softegg/Talkie-DIY-Synth-Kit/docs/PCB Front + back everything.PNG

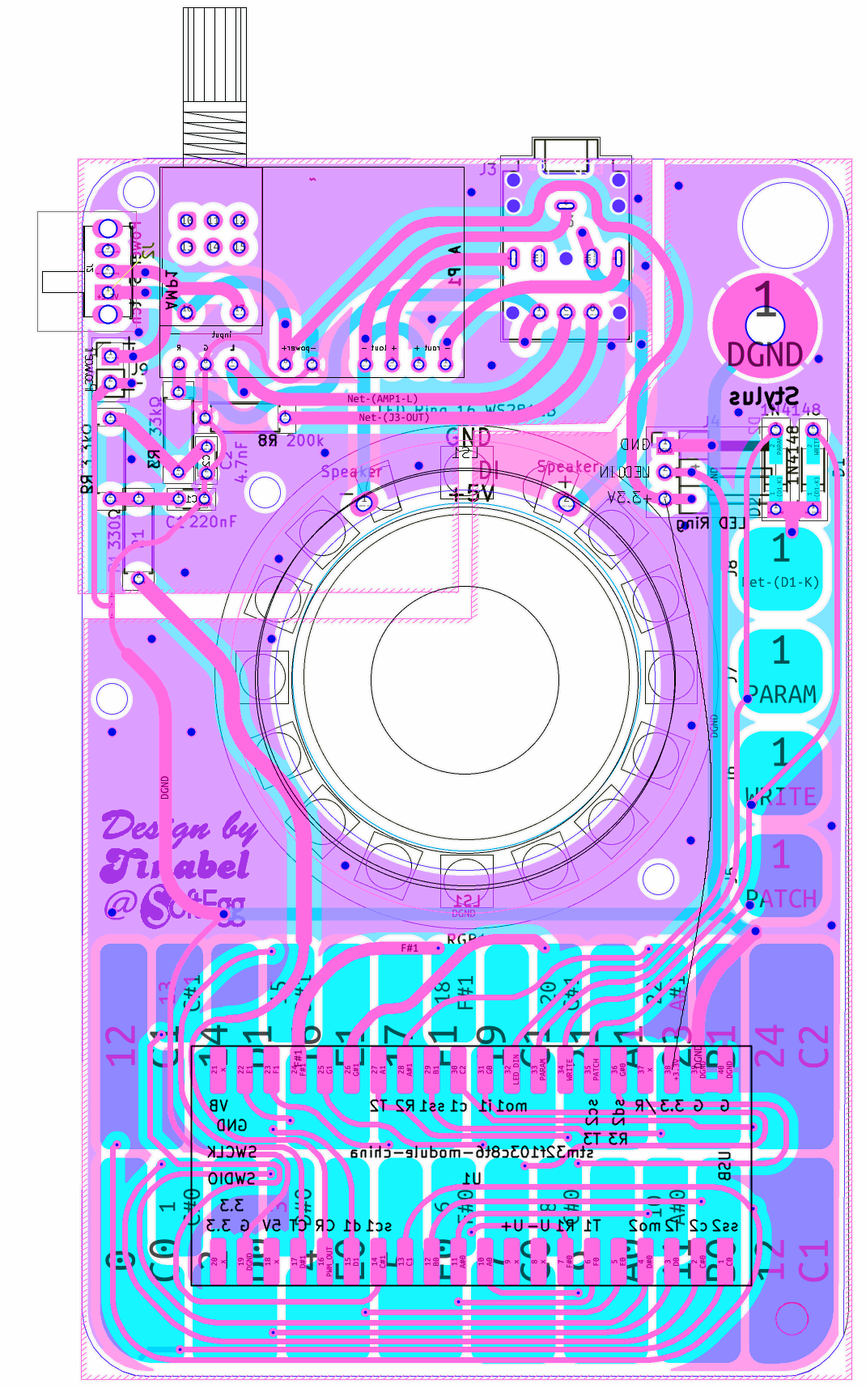
docs/PCB Front + back everything.PNG
