softegg/Talkie-DIY-Synth-Kit/renders/X-DaysSynth-Back.png

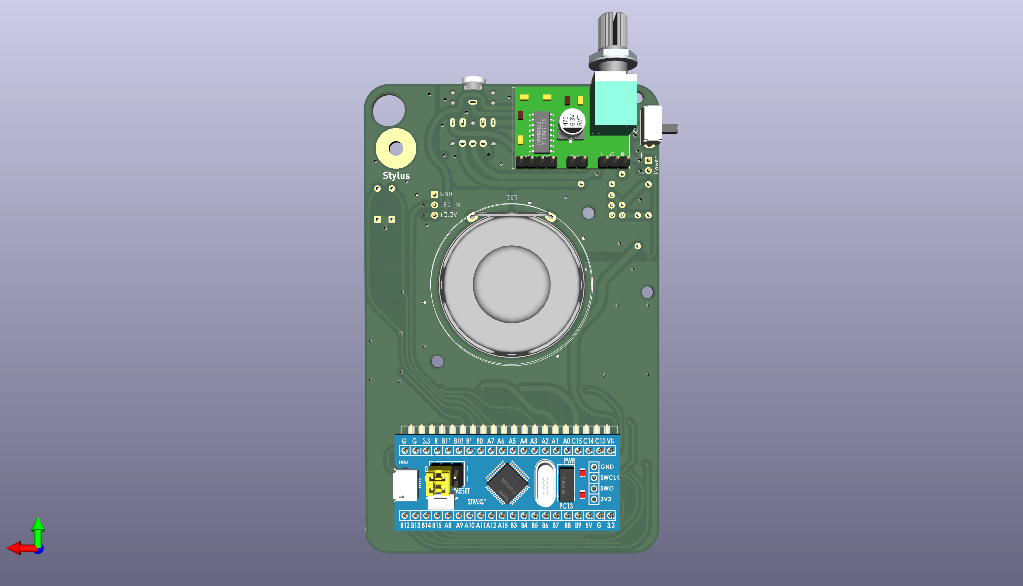
renders/X-DaysSynth-Back.png
