softegg/Talkie-DIY-Synth-Kit/renders/X-DaysSynth-Front-transparent.png

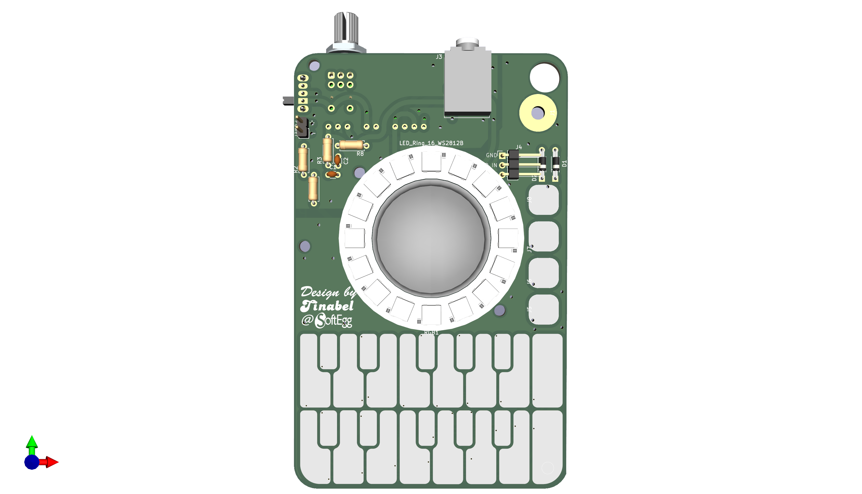
renders/X-DaysSynth-Front-transparent.png
