softegg/Talkie-DIY-Synth-Kit/docs/Back Parts Placement.PNG

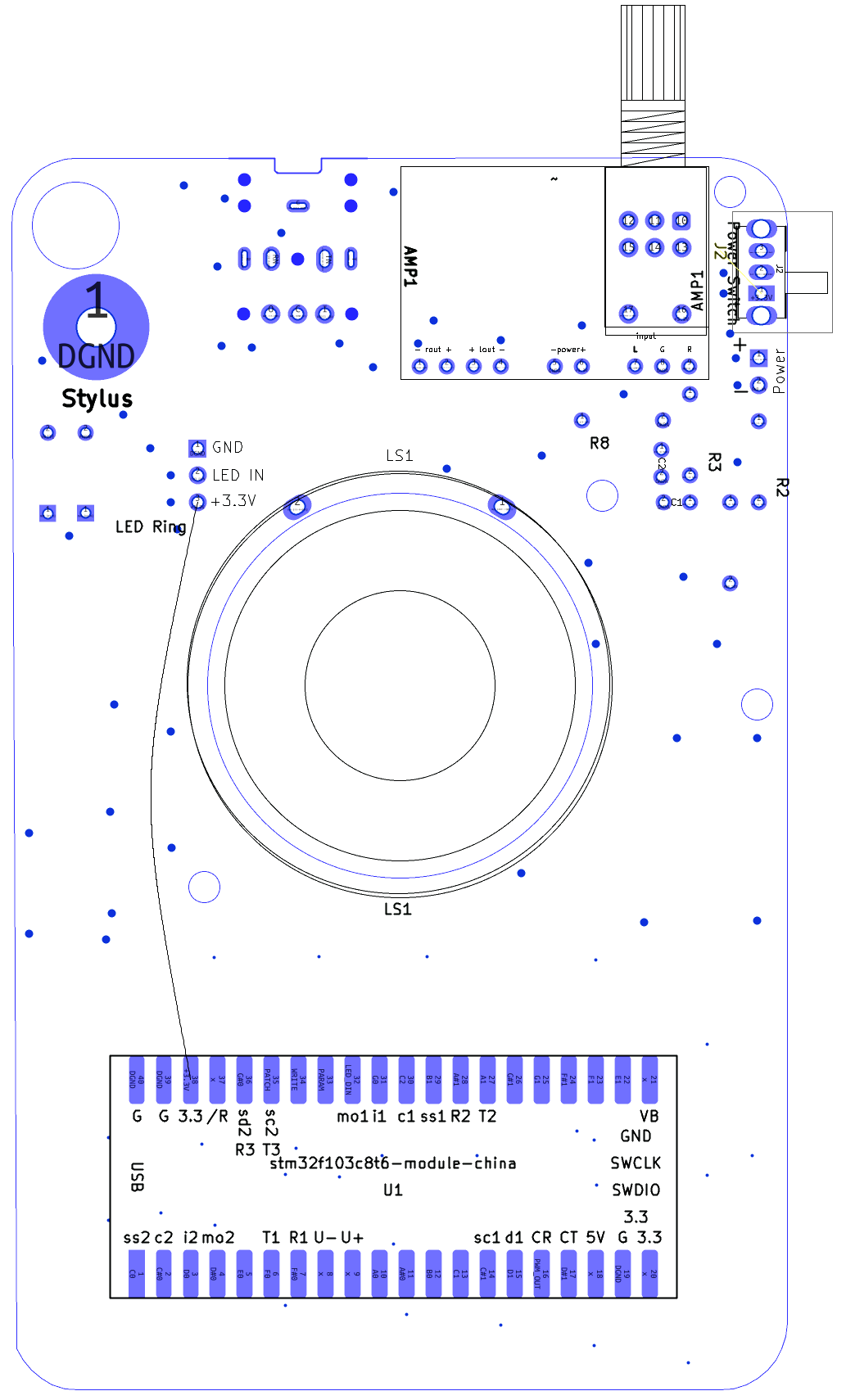
docs/Back Parts Placement.PNG
