softegg/Talkie-DIY-Synth-Kit/docs/Front Parts Placement.PNG

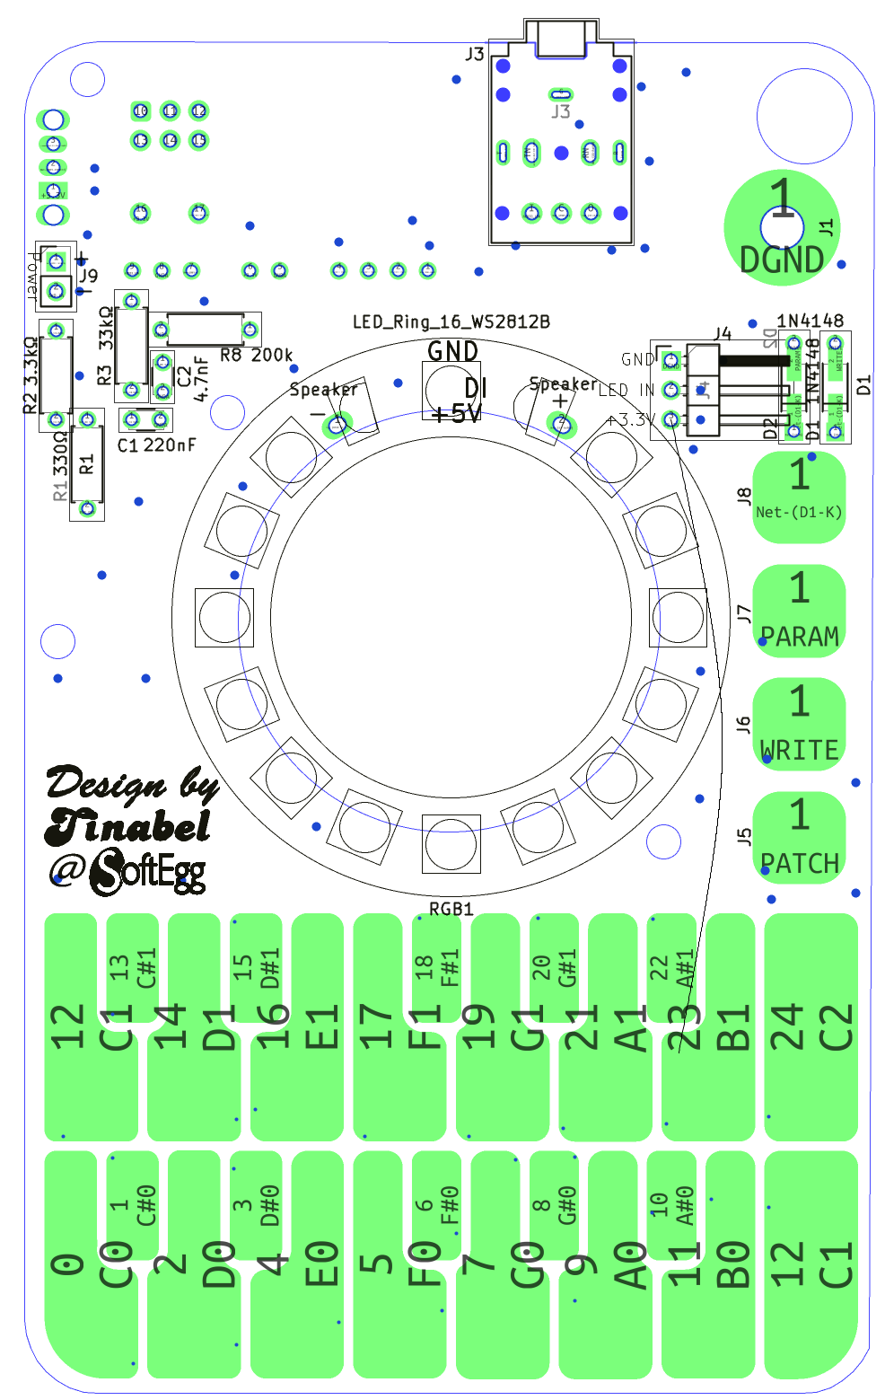
docs/Front Parts Placement.PNG
