softegg/Talkie-DIY-Synth-Kit/docs/assembly pics/Step 0 Bodge cut 1.jpg

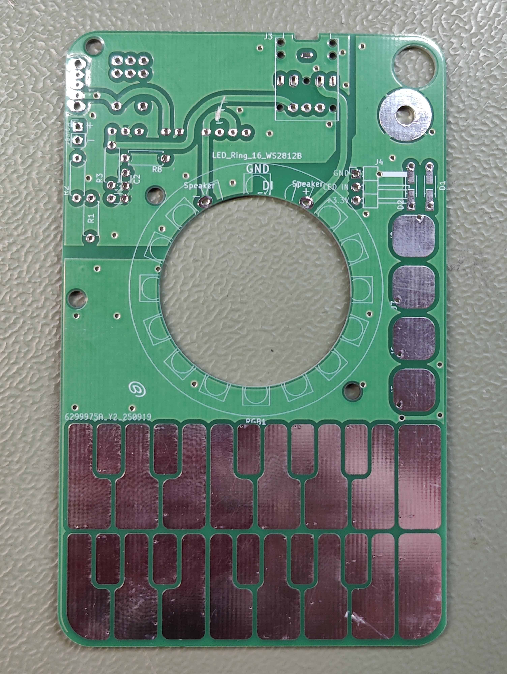
docs/assembly pics/Step 0 Bodge cut 1.jpg
