softegg/Talkie-DIY-Synth-Kit/docs/assembly pics/Step 0 Bodge Cut 2 close up.jpg

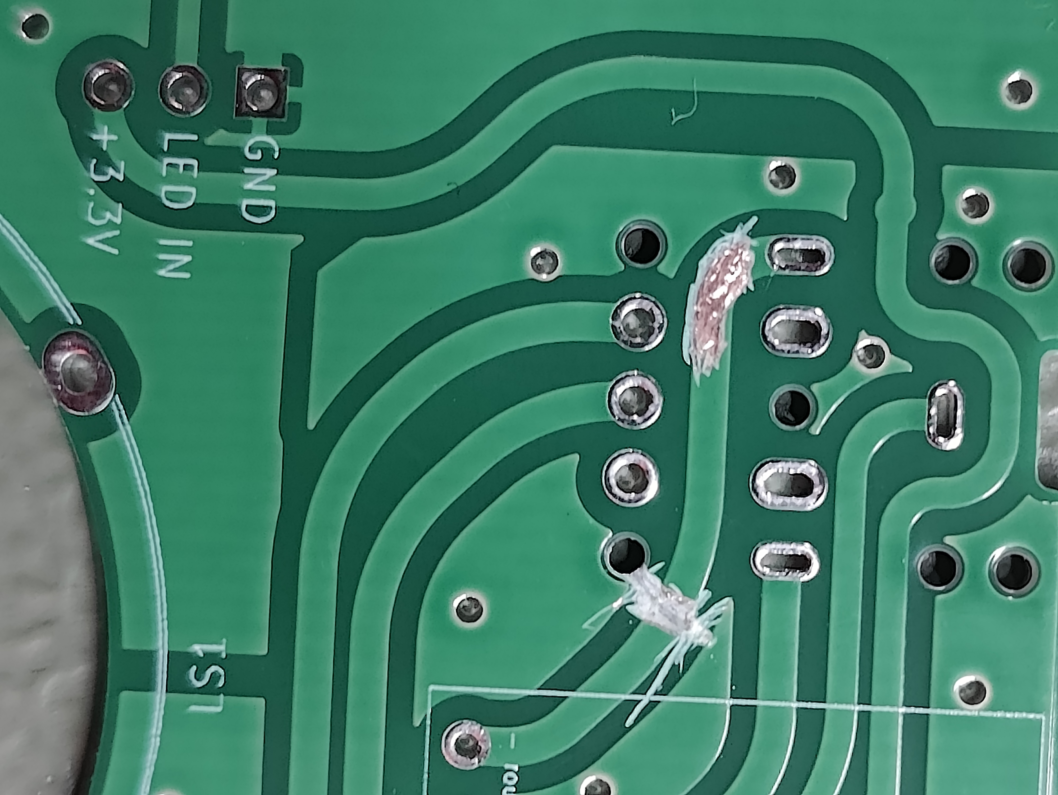
docs/assembly pics/Step 0 Bodge Cut 2 close up.jpg
