softegg/Talkie-DIY-Synth-Kit/docs/assembly pics/Step 1 Resistors.jpg

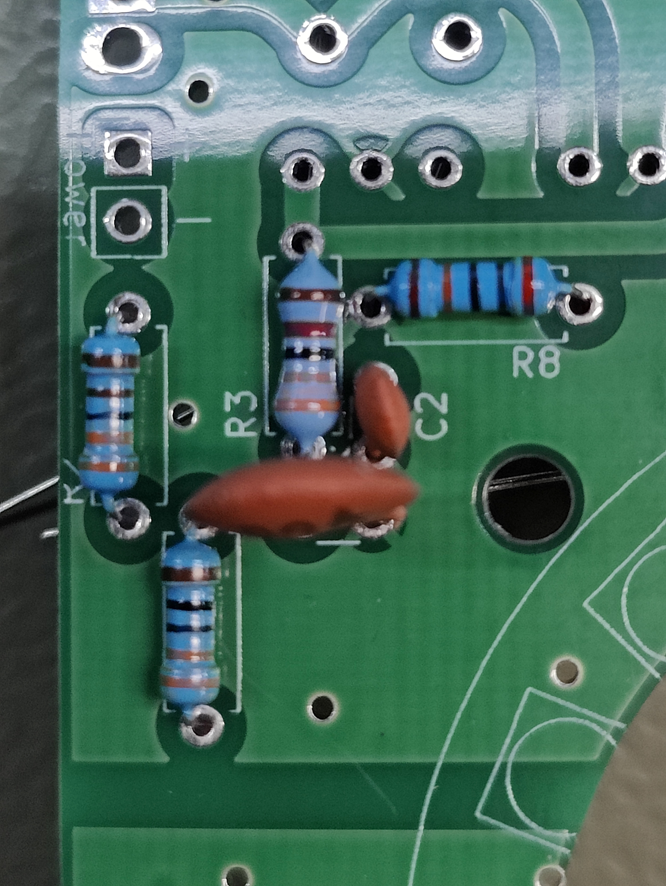
docs/assembly pics/Step 1 Resistors.jpg
