softegg/Talkie-DIY-Synth-Kit/docs/assembly pics/Step 4 Headphone Jack.jpg

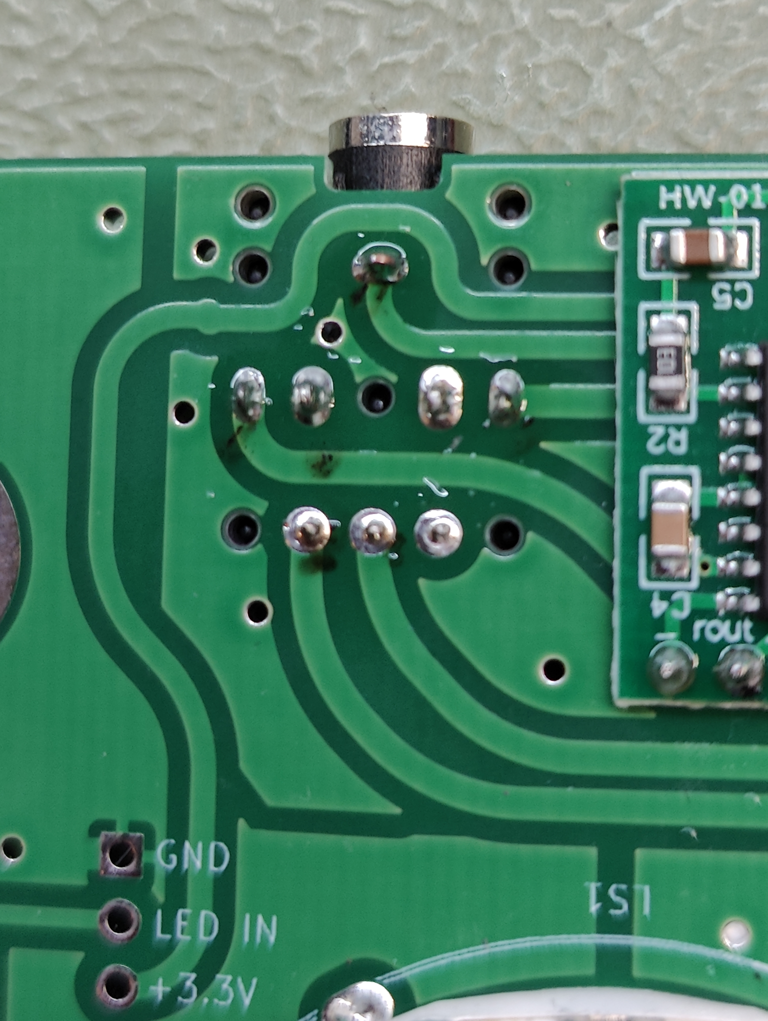
docs/assembly pics/Step 4 Headphone Jack.jpg
